ImStuBTW/chonkv/cases/keyboard_stl.stl

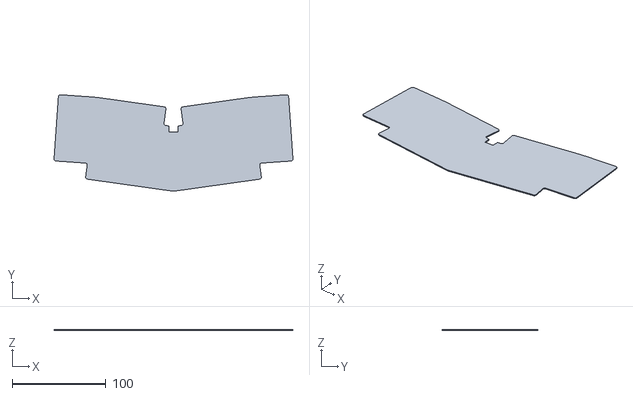
[picture p21: CAD file, 2023-02-19]
cases/keyboard_stl.stl
255.5 x 103.1 x 1.00
