ImStuBTW/chonkv/outlines/insert_group.dxf

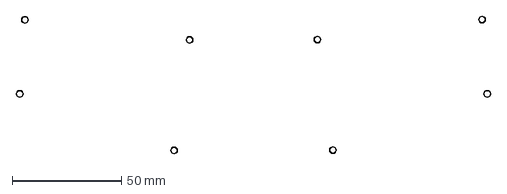
[picture p22: CAD file, 2023-02-19]
outlines/insert_group.dxf
216.9 x 62.8 mm
