ImStuBTW/chonkv/outlines/standoff_group.dxf

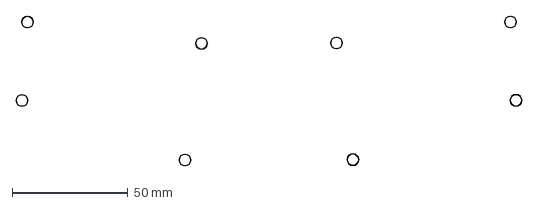
[picture p23: CAD file, 2023-02-19]
outlines/standoff_group.dxf
218.9 x 64.8 mm
