ImStuBTW/chonkv/outlines/border_raw.dxf

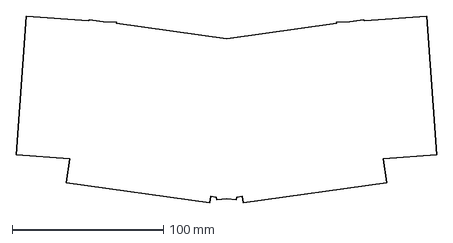
[picture p24: CAD file, 2022-12-28]
outlines/border_raw.dxf
278.2 x 123.6 mm
