ImStuBTW/chonkv/outlines/power_gap.dxf

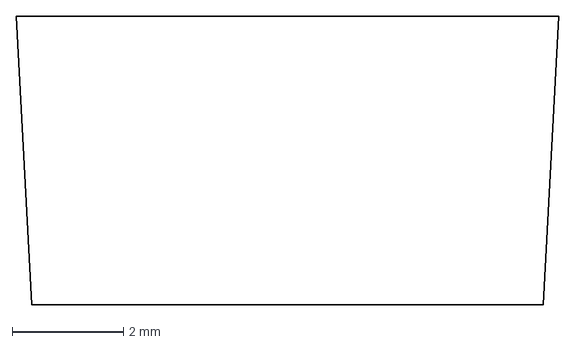
[picture p25: CAD file, 2022-12-28]
outlines/power_gap.dxf
9.76 x 5.19 mm
