ImStuBTW/chonkv/outlines/gaps.dxf

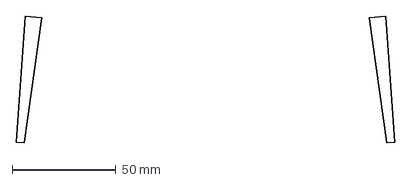
[picture p26: CAD file, 2022-12-28]
outlines/gaps.dxf
182.6 x 61.2 mm
